Lannakin/fan-controller-pico/misc/img/2d-f-cu.png

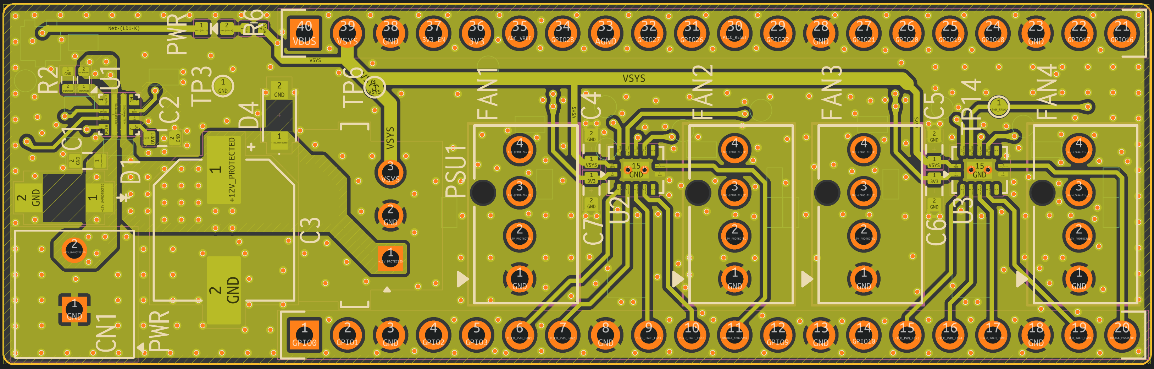
misc/img/2d-f-cu.png
